63ani/ACBS/3D Prints/x_plate.stl

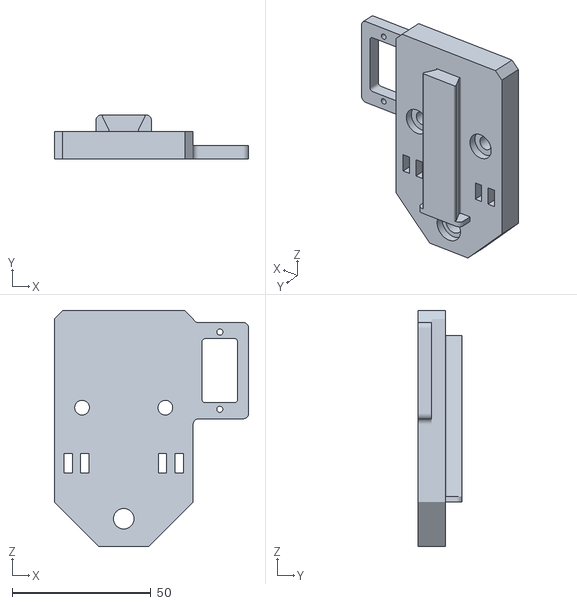
[picture p28: CAD file, 2024-01-20]
3D Prints/x_plate.stl
70.0 x 16.0 x 85.0
