63ani/ACBS/3D Prints/_Chess_Pieces15_PAWN.stl

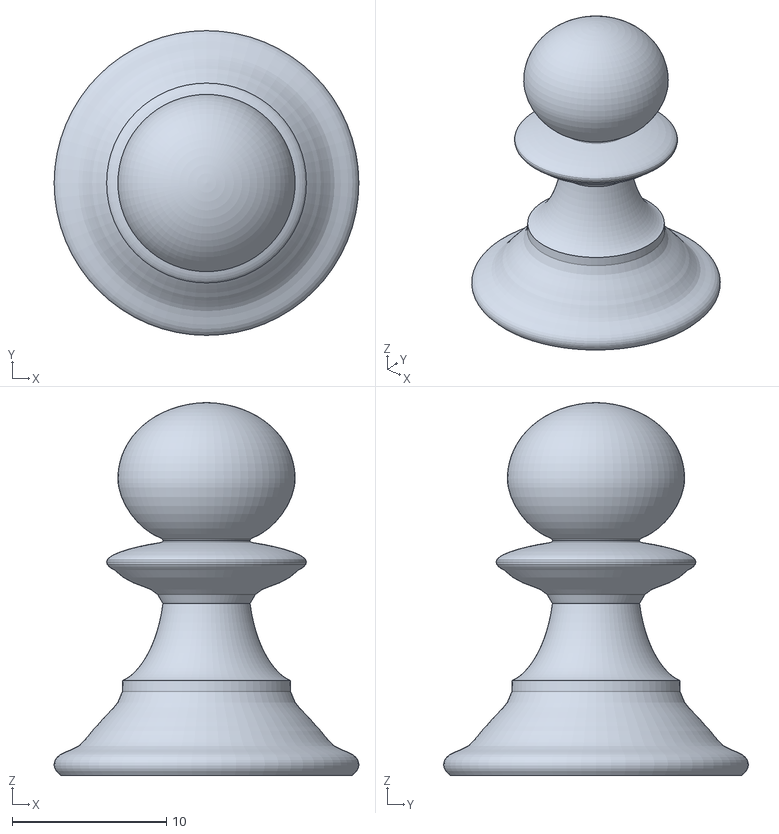
[picture p29: CAD file, 2024-01-20]
3D Prints/_Chess_Pieces15_PAWN.stl
19.8 x 19.8 x 24.2
