63ani/ACBS/3D Prints/spacer.stl

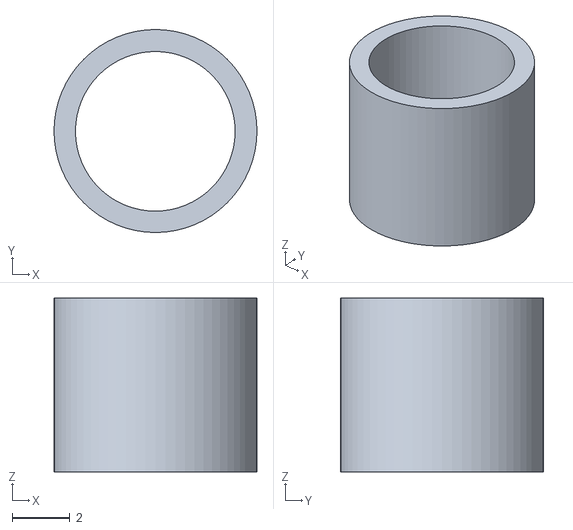
[picture p30: CAD file, 2024-01-20]
3D Prints/spacer.stl
7.00 x 7.00 x 6.00
