63ani/ACBS/pythonProject/ChessBot.py

import random

# A map of piece to score value -> Standard chess scores
pieceScore = {'K': 0, "P": 1, "N": 3, "B": 3, "R": 5, "Q": 9}   #making King = 0, as no one can actually take the king

# Knight Sore according to position -> score reduces as we move towards edges
knightScores = [[1, 1, 1, 1, 1, 1, 1, 1],
                [1, 2, 2, 2, 2, 2, 2, 1],
                [1, 2, 3, 3, 3, 3, 2, 1],
                [1, 2, 3, 4, 4, 3, 2, 1],
                [1, 2, 3, 4, 4, 3, 2, 1],
                [1, 2, 3, 3, 3, 3, 2, 1],
                [1, 2, 2, 2, 2, 2, 2, 1],
                [1, 1, 1, 1, 1, 1, 1, 1]]

bishopScores = [[4, 3, 2, 1, 1, 2, 3, 4],
                [3, 4, 3, 2, 2, 3, 4, 3],
                [2, 3, 4, 3, 3, 4, 3, 2],
                [1, 2, 3, 4, 4, 3, 2, 1],
                [1, 2, 3, 4, 4, 3, 2, 1],
                [2, 3, 4, 3, 3, 4, 3, 2],
                [3, 4, 3, 2, 2, 3, 4, 3],
                [4, 3, 2, 1, 1, 2, 3, 4]]

queenScores = [[1, 1, 1, 3, 1, 1, 1, 1],
               [1, 2, 3, 3, 3, 1, 1, 1],
               [1, 4, 3, 3, 3, 4, 2, 1],
               [1, 2, 3, 3, 3, 2, 2, 1],
               [1, 2, 3, 3, 3, 2, 2, 1],
               [1, 4, 3, 3, 3, 4, 2, 1],
               [1, 1, 2, 3, 3, 1, 1, 1],
               [1, 1, 1, 3, 1, 1, 1, 1]]

rookScores = [[4, 3, 4, 4, 4, 4, 3, 4],
               [4, 4, 4, 4, 4, 4, 4, 4],
               [1, 1, 2, 3, 3, 2, 1, 1],
               [1, 2, 3, 4, 4, 3, 2, 1],
               [1, 2, 3, 4, 4, 3, 2, 1],
               [1, 1, 2, 3, 3, 2, 1, 1],
               [4, 4, 4, 4, 4, 4, 4, 4],
               [4, 3, 4, 4, 4, 4, 3, 4]]

whitePawnScores = [[8, 8, 8, 8, 8, 8, 8, 8],
                   [8, 8, 8, 8, 8, 8, 8, 8],
                   [5, 6, 6, 7, 7, 6, 6, 5],
                   [2, 3, 3, 5, 5, 3, 3, 2],
                   [1, 2, 3, 3, 2, 2, 1, 1],
                   [1, 1, 2, 3, 3, 2, 1, 1],
                   [1, 1, 1, 0, 0, 1, 1, 1],
                   [0, 0, 0, 0, 0, 0, 0, 0]]

blackPawnScores = [[0, 0, 0, 0, 0, 0, 0, 0],
                   [1, 1, 1, 0, 0, 1, 1, 1],
                   [1, 1, 2, 3, 3, 2, 1, 1],
                   [1, 2, 3, 3, 2, 2, 1, 1],
                   [2, 3, 3, 5, 5, 3, 3, 2],
                   [5, 6, 6, 7, 7, 6, 6, 5],
                   [8, 8, 8, 8, 8, 8, 8, 8],
                   [8, 8, 8, 8, 8, 8, 8, 8]]

piecePositionScores = {'N': knightScores, "Q": queenScores, "B": bishopScores, "R": rookScores, 'wP': whitePawnScores, 'bP' : blackPawnScores}

CHECKMATE = 1000    # if you lead to checkmate you win -> hence max attainable score
STALEMATE = 0       # If you can win(capture opponent's piece) avoid it but if you loosing(opponent can give you Checkmate) try it hence 0 and not -1000
DEPTH = 2           # Depth for recursive calls
'''
    Function to calculate RANDOM move from the list of valid moves.
'''
def findRandomMove(validMoves):
    if len(validMoves) > 0:
        return validMoves[random.randint(0, len(validMoves) - 1)]


'''
    Function to find the BEST move from the list of valid moves
'''
def findBestMove(gs, validMoves):
    turnMultiplier = 1 if gs.whiteToMove else -1    # for allowing AI to play as any color
    playerMaxScore = -CHECKMATE    # as AI is playing Black this is the worst possible score -> AI will start from worst and try to improve
    bestMove = None
    random.shuffle(validMoves)
    for playerMove in validMoves:   # not assigning colors so AI can play as both: playerMove -> move of the current player || opponentMove -> opponent's move
        gs.makeMove(playerMove)
        opponentMinScore = CHECKMATE
        opponentMoves = gs.getValidMoves()
        if gs.checkMate:
            gs.undoMove()
            return playerMove
        elif gs.staleMate:
            opponentMinScore = STALEMATE
        else:
            for opponentMove in opponentMoves:
                gs.makeMove(opponentMove)
                gs.getValidMoves()
                if gs.checkMate:
                    score = -CHECKMATE
                elif gs.staleMate:
                    score = STALEMATE
                else:
                    score = turnMultiplier * materialScore(gs.board)
                if score < opponentMinScore:
                    opponentMinScore = score
                gs.undoMove()
        if playerMaxScore < opponentMinScore:
            playerMaxScore = opponentMinScore
            bestMove = playerMove
        gs.undoMove()
    return bestMove

'''
   Helper method to call recursion for the 1st time 
'''
def findBestMoveMinMax(gs, validMoves):
    global nextMove     # to find the next move
    nextMove = None
    random.shuffle(validMoves)
    findMoveNegaMaxAlphaBetaPruning(gs, validMoves, DEPTH, -CHECKMATE, CHECKMATE, 1 if gs.whiteToMove else -1)     # For using Nega Max Algorithm with Alpha Beta Pruning
    # findMoveNegaMax(gs, validMoves, DEPTH, 1 if gs.whiteToMove else -1)     # For using Nega Max Algorithm
    # findMoveMinMax(gs, validMoves, DEPTH, gs.whiteToMove)     # For using Min-Max Algorithm
    return nextMove

'''
    Find the best move based on material itself
'''
def findMoveMinMax(gs, validMoves, depth, whiteToMove):
    if depth == 0:      # We have reached the bottom of the tree -> with fixed depth == DEPTH
        return boardScore(gs)   #return the score

    global nextMove
    if gs.whiteToMove:  # Try to maximise score
        maxScore = -CHECKMATE
        for move in validMoves:
            gs.makeMove(move)
            nextMoves = gs.getValidMoves()
            score = findMoveMinMax(gs, nextMoves, depth-1, False)
            if score > maxScore:
                maxScore = score
                if depth == DEPTH:
                    nextMove = move
            gs.undoMove()
        return maxScore
    else:   # Try to minimise score
        minScore = CHECKMATE
        for move in validMoves:
            gs.makeMove(move)
            nextMoves = gs.getValidMoves()
            score = findMoveMinMax(gs, nextMoves, depth-1, True)
            if score < minScore:
                minScore = score
                if depth == DEPTH:
                    nextMove = move
            gs.undoMove()
        return minScore

'''
BEST Move calculator using NegaMax Algorithm
'''
def findMoveNegaMax(gs, validMoves, depth, turnMultiplier):
    global nextMove
    if depth == 0:
        return turnMultiplier * boardScore(gs)

    maxScore = -CHECKMATE
    for move in validMoves:
        gs.makeMove(move)
        nextMoves = gs.getValidMoves()
        score = -findMoveNegaMax(gs, nextMoves, depth-1, -turnMultiplier)   # negative for NEGA Max
        if score > maxScore:
            maxScore = score
            if depth == DEPTH:
                nextMove = move
        gs.undoMove()
    return score

'''
BEST Move calculator using NegaMax Algorithm along with  Alpha Beta Pruning
'''
def findMoveNegaMaxAlphaBetaPruning(gs, validMoves, depth, alpha, beta, turnMultiplier):
    global nextMove
    if depth == 0:
        return turnMultiplier * boardScore(gs)

    # Move Ordering -> (TODO)
        # Traverse better moves 1st -> ones with checks and captures -> will lead to more pruning and more optimised algorithm
    maxScore = -CHECKMATE
    for move in validMoves:
        gs.makeMove(move)
        nextMoves = gs.getValidMoves()
        score = -findMoveNegaMaxAlphaBetaPruning(gs, nextMoves, depth-1, -beta, -alpha, -turnMultiplier)   # negative for NEGA Max
        if score > maxScore:
            maxScore = score
            if depth == DEPTH:
                nextMove = move
        gs.undoMove()
        if maxScore > alpha:
            alpha = maxScore
        if alpha >= beta:
            break
    return maxScore


'''
    better scoring algorithm with considering checks and stalemates. 
    +ve score good for white
    -ve score good for black
'''
def boardScore(gs):
    if gs.checkMate:
        if gs.whiteToMove:
            return -CHECKMATE   # BLACK WINS
        else:
            return CHECKMATE
    if gs.staleMate:
        return STALEMATE
    score = 0
    for row in range(len(gs.board)):
        for col in range(len(gs.board[row])):
            square = gs.board[row][col]
            if square != '--':
                #score it positionally
                piecePositionScore = 0

                if square[1] != 'K':
                    if square[1] == 'P':
                        piecePositionScore = piecePositionScores[square][row][col]
                    else:
                        piecePositionScore = piecePositionScores[square[1]][row][col]
                if square[0] == 'w':
                    score += pieceScore[square[1]] + piecePositionScore * 0.1   # 0.1 to make the game less positional
                elif square[0] == 'b':
                    score -= pieceScore[square[1]] + piecePositionScore * 0.1
    return score

'''
    Gives the score of the board according to the material on it -> White piece positive material and Black piece negative material.
    Assuming that Human is playing White and BOT is playing black
'''
def materialScore(board):
    score = 0
    for row in board:
        for square in row:
            if square[0] == 'w':
                score += pieceScore[square[1]]
            elif square[0] == 'b':
                score -= pieceScore[square[1]]
    return score
